antonynyt/head-md-soft-robotics/presskit/medias/pulmo-2.jpg

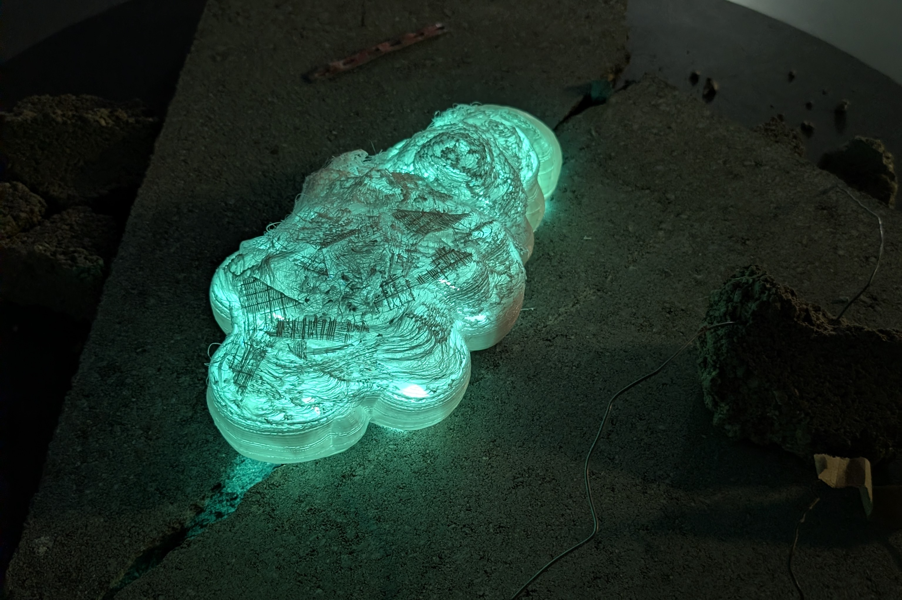
presskit/medias/pulmo-2.jpg
