antonynyt/head-md-soft-robotics/process/attachments/2026-01-12-fusion.jpg

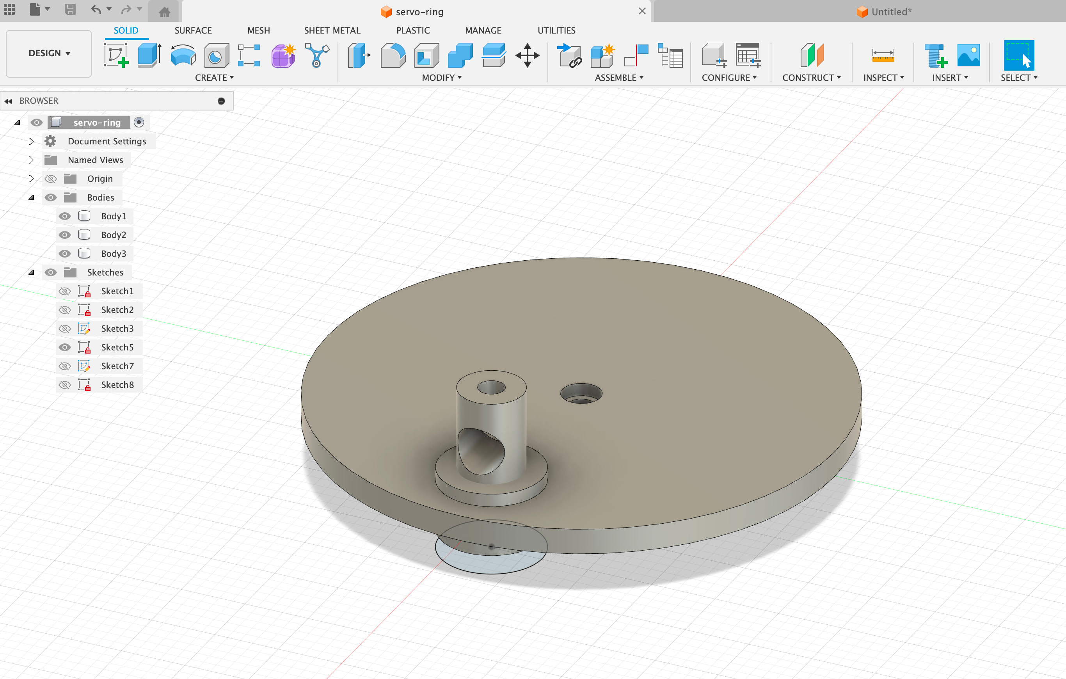
process/attachments/2026-01-12-fusion.jpg
