antonynyt/head-md-soft-robotics/process/attachments/2026-01-12-proto-lights-trought.jpg

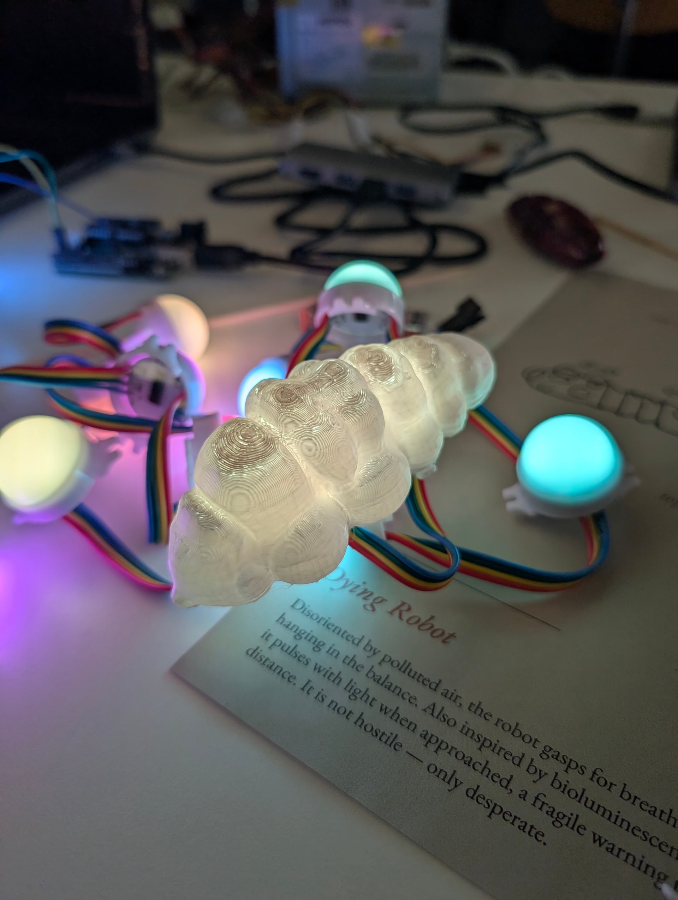
process/attachments/2026-01-12-proto-lights-trought.jpg
