antonynyt/head-md-soft-robotics/process/attachments/2026-01-14-mecanism.jpg

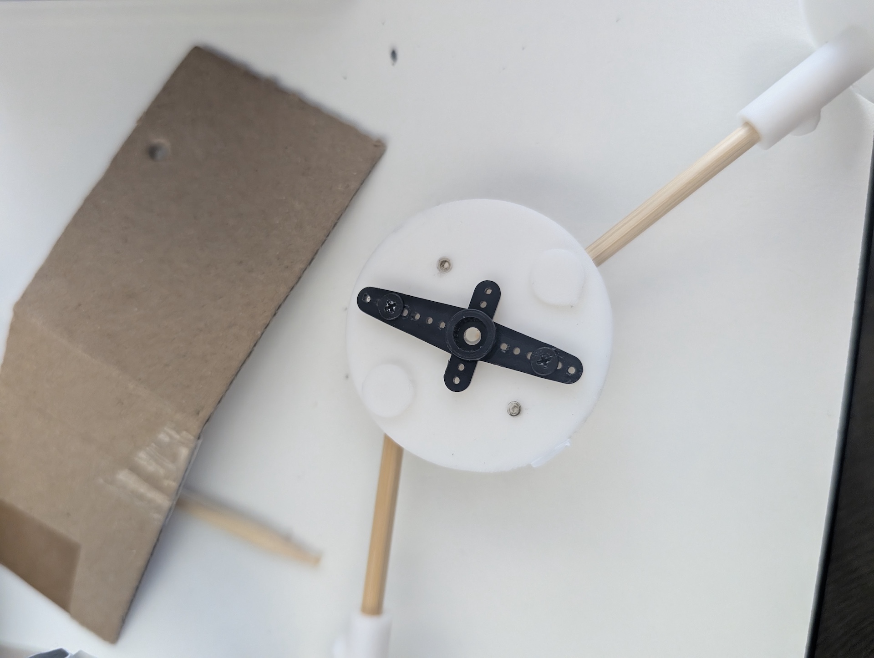
process/attachments/2026-01-14-mecanism.jpg
